dhairyashah1/USBee32-S2/assets/screenshots/2-layer/back.png

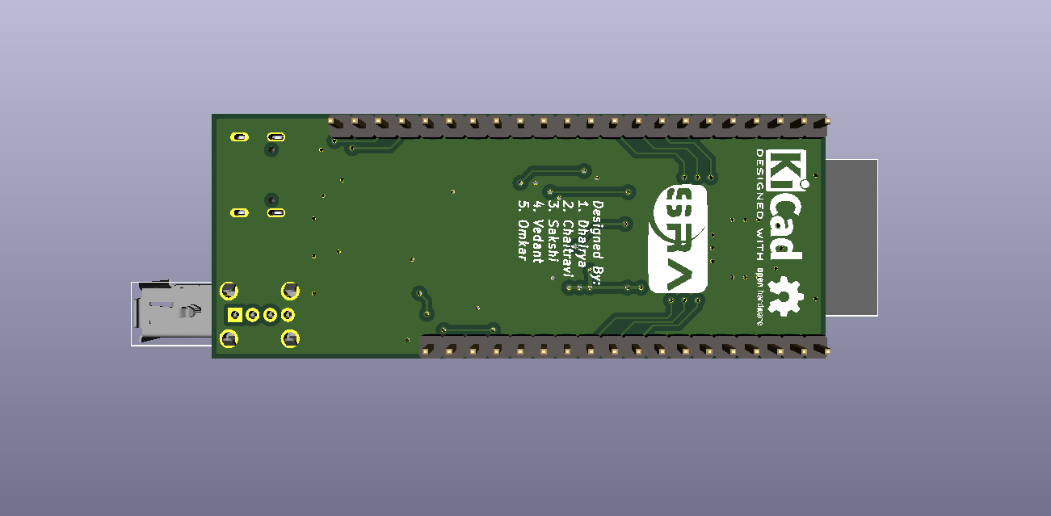
assets/screenshots/2-layer/back.png
