dhairyashah1/USBee32-S2/assets/screenshots/2-layer/frontside2.png

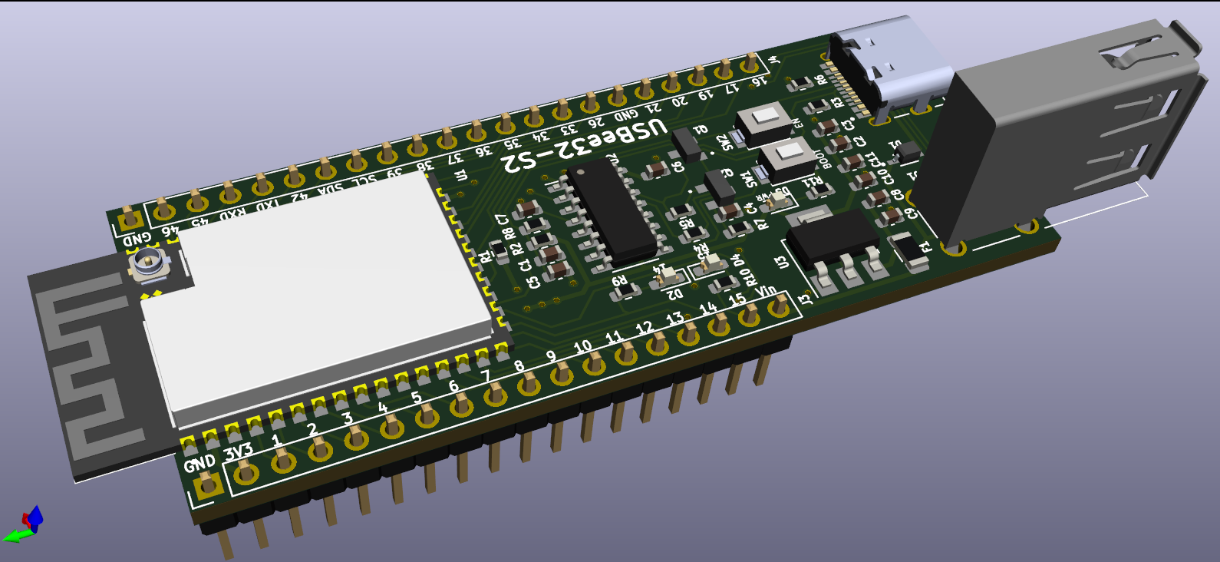
assets/screenshots/2-layer/frontside2.png
