dhairyashah1/USBee32-S2/assets/screenshots/4-layer/bcu_layer.png

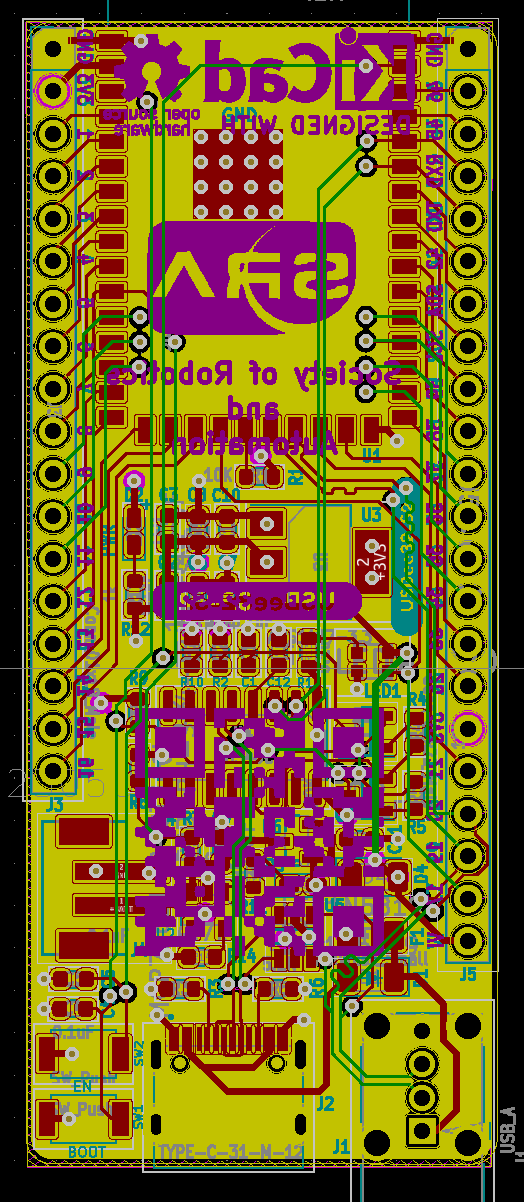
assets/screenshots/4-layer/bcu_layer.png
