dhairyashah1/USBee32-S2/assets/screenshots/4-layer/general2.png

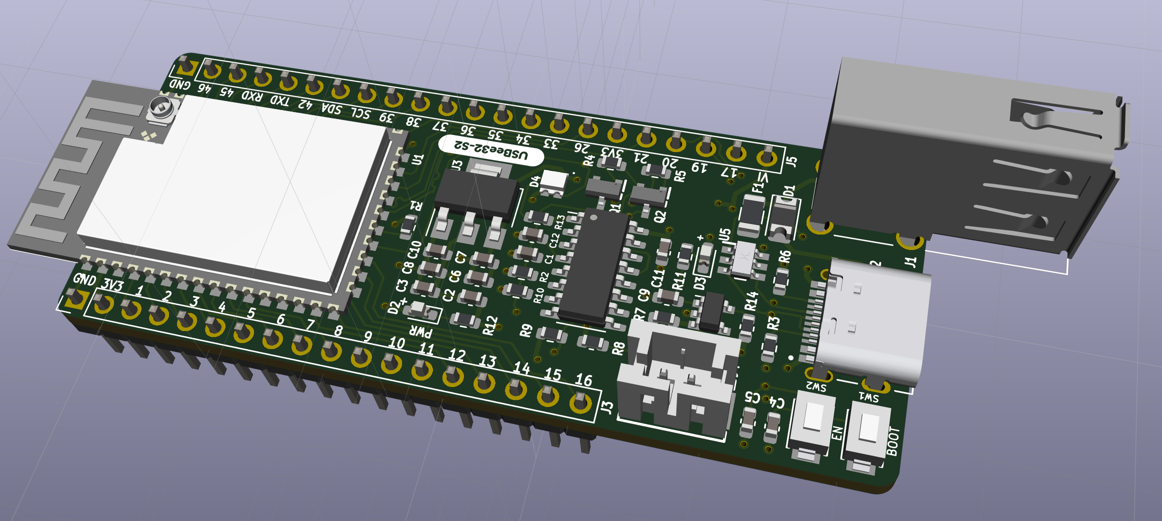
assets/screenshots/4-layer/general2.png
