dhairyashah1/USBee32-S2/assets/screenshots/4-layer/gnd_layer.png

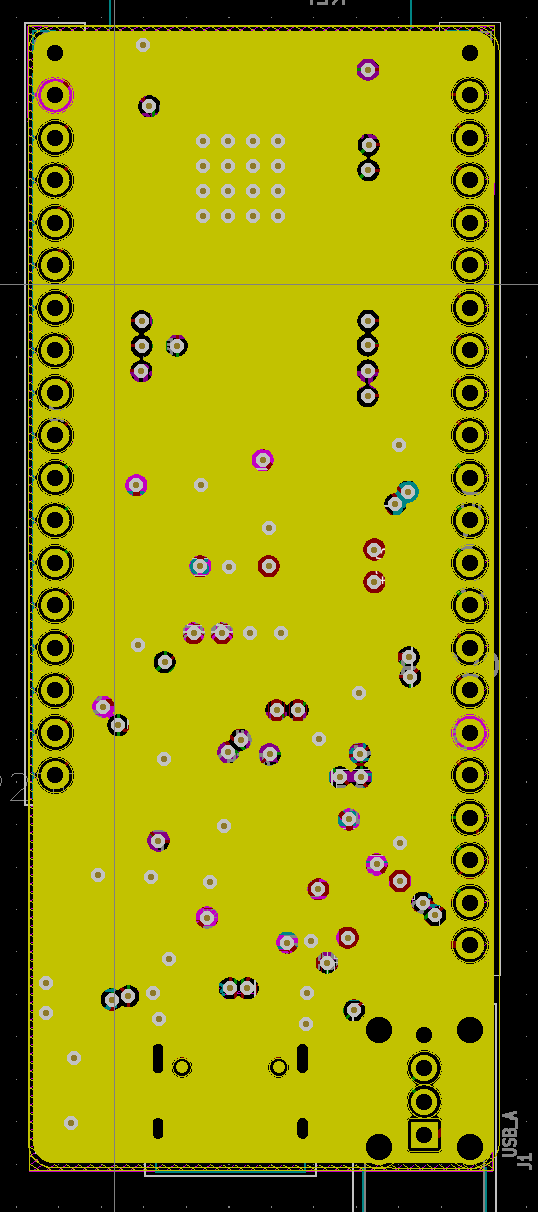
assets/screenshots/4-layer/gnd_layer.png
