dhairyashah1/USBee32-S2/assets/screenshots/qr/usbee32-s2-qr.png

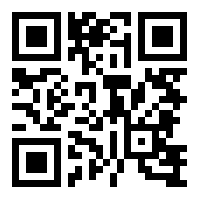
assets/screenshots/qr/usbee32-s2-qr.png
