dhairyashah1/USBee32-S2/USBee32-S2/component_libraries/USB-A-3D/Renderings/USB-A 111 (vertical on plate).png

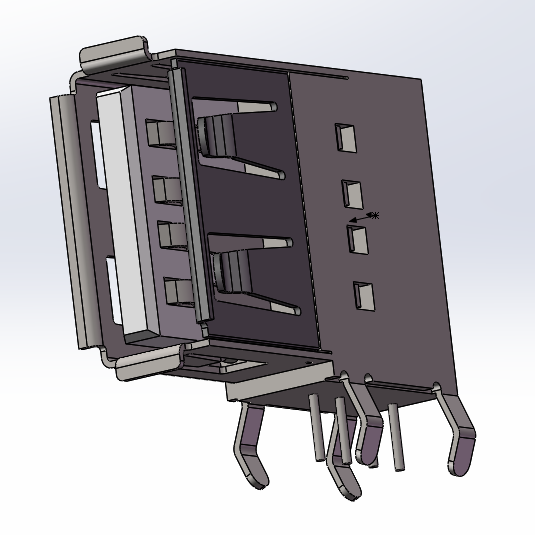
USBee32-S2/component_libraries/USB-A-3D/Renderings/USB-A 111 (vertical on plate).png
