dhairyashah1/USBee32-S2/renders/v.2/usbee32-s2.FCStd

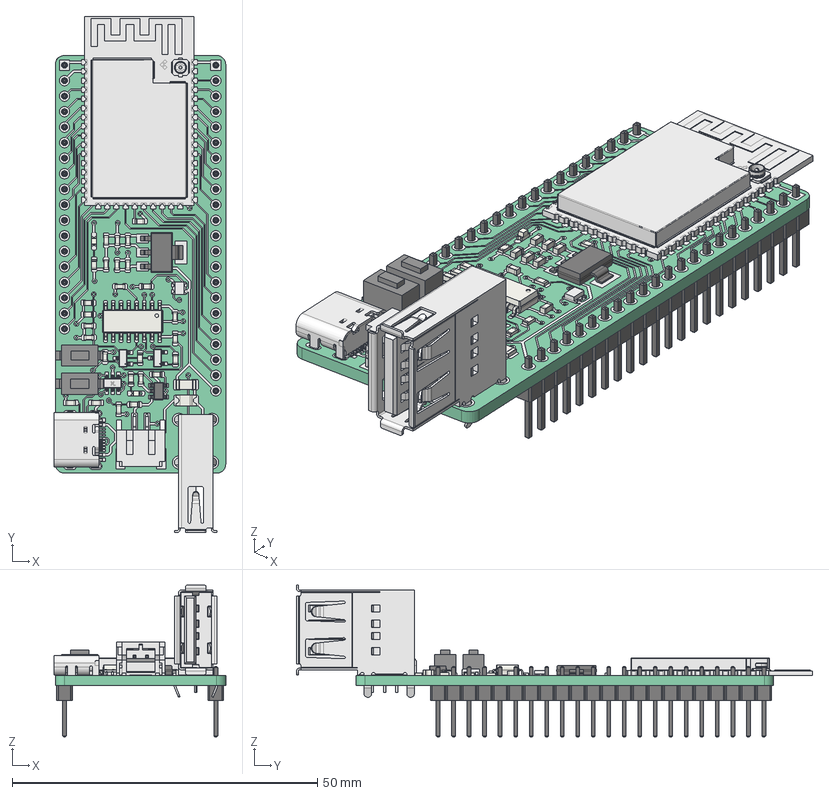
[picture p42: CAD file, 2021-07-15, an earlier design]
renders/v.2/usbee32-s2.FCStd
28.1 x 84.5 x 24.9 mm
Pcb_9a
topTracks_9a
botTracks_9a
U1_ESP32-S2-WROVER_60C23B21
U4_SOT_23_5_60B7CB05
J2_TYPE-C-31-M-12_60C23E4A
D1_D_1206_60B7D0F0
R10_R_0603_1608Metric_60ABBC6C
D3_LED_0603_1608Metric_Castellated_60B7CE11
U3_BC847,215_60ABADBB
U2_BC847,215_60ABA81C
R8_R_0603_1608Metric_60B7DF5D
R7_R_0603_1608Metric_60A08701
J4_S2B-PH-SM4-TB_LF__SN__60BE4523
D4_WS2812-2020_60BF3307[2]
C9_C_0603_1608Metric_60A08420
IC1_IP4220CZ6,125_60ABB8B8
J1_USB-A 111 (vertical on plate)_60ABB31E
R14_R_0603_1608Metric_60AC0056
R12_R_0603_1608Metric_60B7C5D6
R11_R_0603_1608Metric_60AB4011
C8_C_0603_1608Metric_60B7D9F7
C6_C_0603_1608Metric_60B7DB26
F1_Fuse_1206_3216Metric_60B7CE77
J5_PinHeader_1x22_P254mm_Vertical_6050A9A6
U6_SOIC_16_39x99mm_P127mm_60AB7F91
C11_C_0603_1608Metric_60B6BBC9
SW2_User Library-KFC-2Pin SMD_60442C51
SW1_User Library-KFC-2Pin SMD_60ABA6D9
R5_R_0603_1608Metric_60B7C8AB
R13_R_0603_1608Metric_60BE3656
J3_PinHeader_1x18_P254mm_Vertical_605098B1
D2_LED_0603_1608Metric_Castellated_60B7D9C3
C10_C_0603_1608Metric_60B89E3D
C4_C_0603_1608Metric_60AB6E2D
C1_C_0603_1608Metric_604935C4
C12_C_0603_1608Metric_60BE381E
R3_R_0603_1608Metric_602B1788
R6_R_0603_1608Metric_60B7C2F6
R1_R_0603_1608Metric_60B83448
R9_R_0603_1608Metric_603C1870
U5_SOT_223_60B7DAEC
R2_R_0603_1608Metric_60ABBBA9
C5_C_0603_1608Metric_60AB99C1
C3_C_0603_1608Metric_60B7DA27
C2_C_0603_1608Metric_60B7DB56
C7_C_0603_1608Metric_60B8A46F
R4_R_0603_1608Metric_60ABAFE2
